efritz09/washiato/Embedded/Washing Cycle Data/Inst_x.png

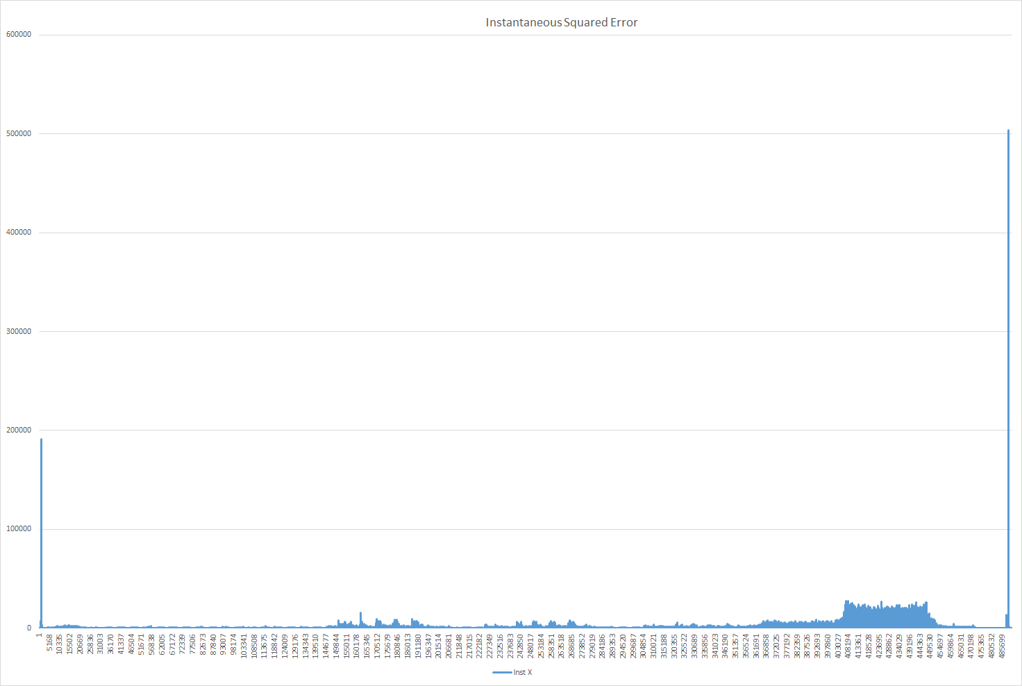
Embedded/Washing Cycle Data/Inst_x.png
