efritz09/washiato/Mechanical Design/COMMUNAL_PARTS/WIFI_HUZZAH.SLDPRT

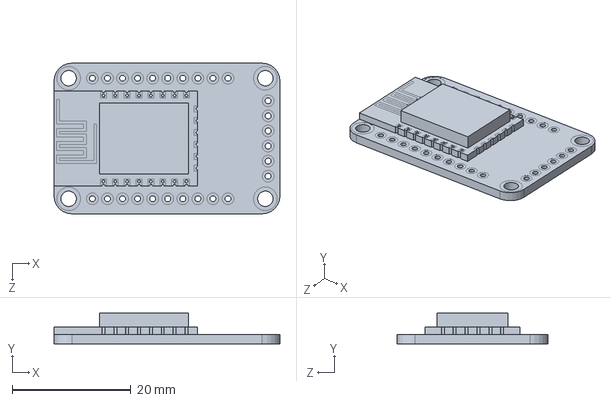
[picture p22: CAD file, 2016-05-10]
Mechanical Design/COMMUNAL_PARTS/WIFI_HUZZAH.SLDPRT
38.1 x 5.18 x 25.4 mm
