efritz09/washiato/Deliverables/CAD/TOP.SLDPRT

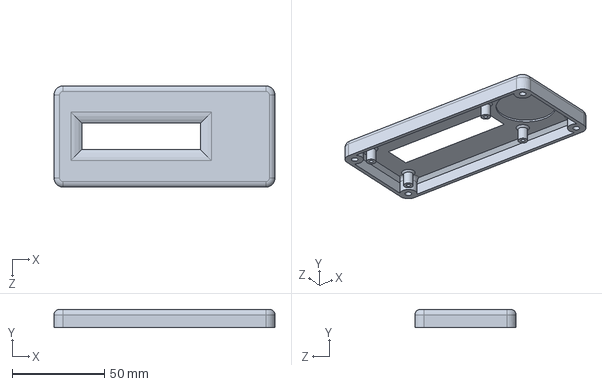
[picture p23: CAD file, 2016-06-02]
Deliverables/CAD/TOP.SLDPRT
120.0 x 10.0 x 55.0 mm
