efritz09/washiato/Mechanical Design/COMMUNAL_PARTS/POLOLU_U3V12F5.SLDPRT

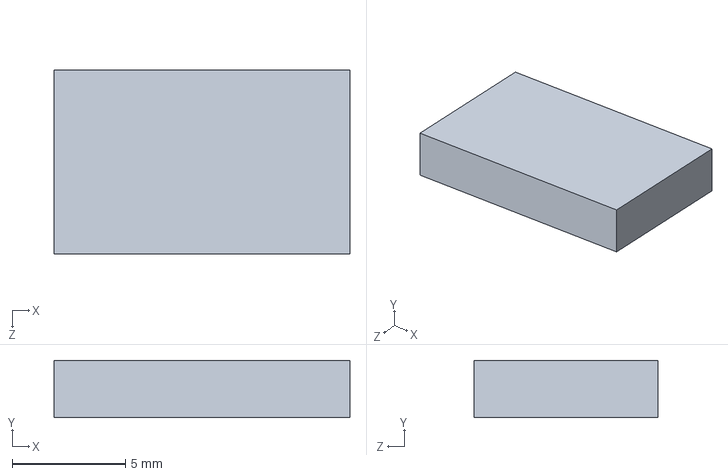
[picture p24: CAD file, 2016-05-10]
Mechanical Design/COMMUNAL_PARTS/POLOLU_U3V12F5.SLDPRT
13.1 x 2.54 x 8.13 mm
