efritz09/washiato/Mechanical Design/COMMUNAL_PARTS/LIMIT_SWITCH.SLDPRT

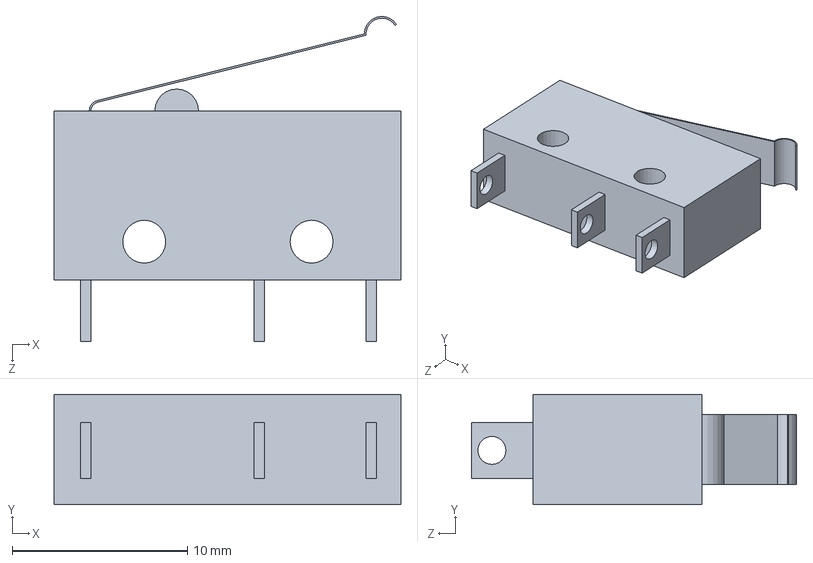
[picture p25: CAD file, 2016-05-10]
Mechanical Design/COMMUNAL_PARTS/LIMIT_SWITCH.SLDPRT
19.8 x 6.30 x 18.6 mm
