efritz09/washiato/Deliverables/CAD/PIN.SLDPRT

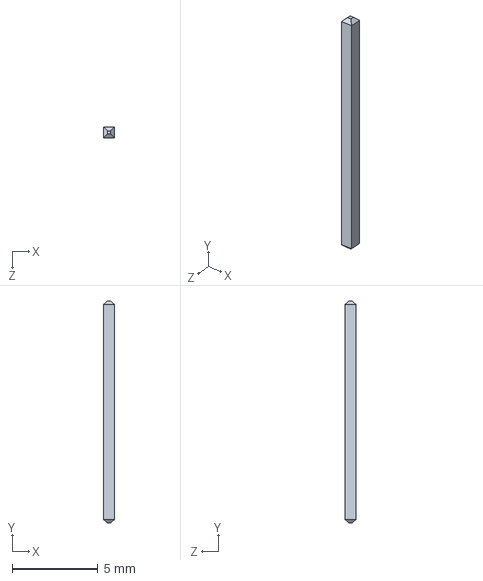
[picture p26: CAD file, 2016-06-02]
Deliverables/CAD/PIN.SLDPRT
0.64 x 12.9 x 0.64 mm
