efritz09/washiato/Deliverables/CAD/BASE.SLDPRT

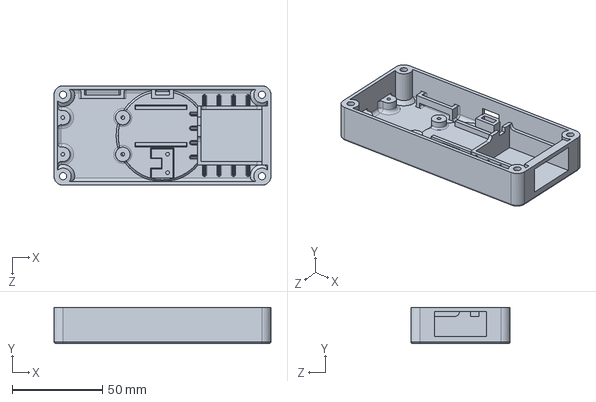
[picture p27: CAD file, 2016-06-02]
Deliverables/CAD/BASE.SLDPRT
120.0 x 20.0 x 55.0 mm
