efritz09/washiato/Deliverables/CAD/SPARKFUN_MMA8452Q_BOARD.SLDPRT

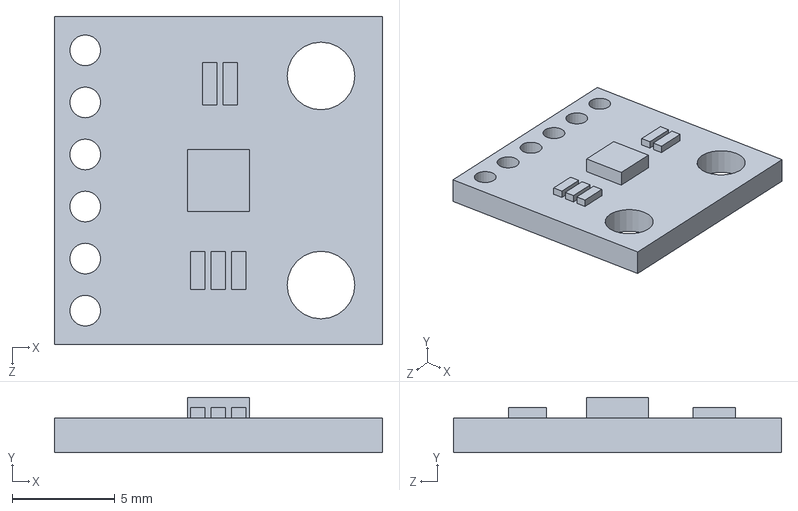
[picture p28: CAD file, 2016-06-02]
Deliverables/CAD/SPARKFUN_MMA8452Q_BOARD.SLDPRT
16.0 x 2.70 x 16.0 mm
