efritz09/washiato/Deliverables/CAD/PIN_HEADER.SLDPRT

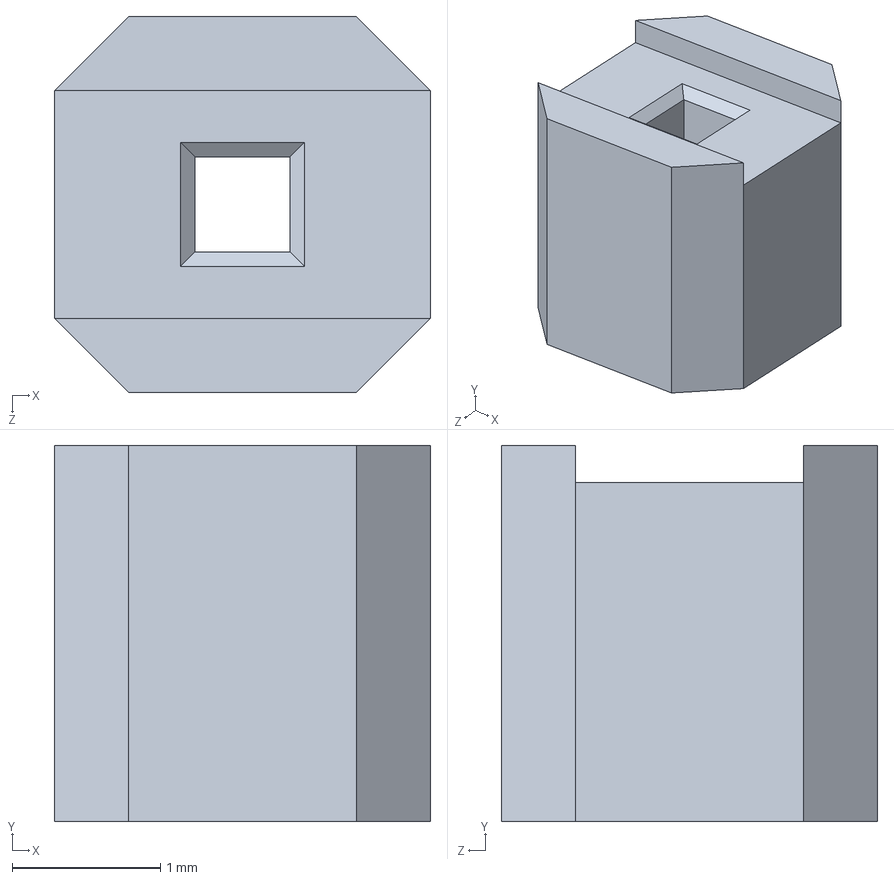
[picture p29: CAD file, 2016-06-02]
Deliverables/CAD/PIN_HEADER.SLDPRT
2.54 x 2.54 x 2.54 mm
