efritz09/washiato/Deliverables/CAD/BATTERY_COVER.SLDPRT

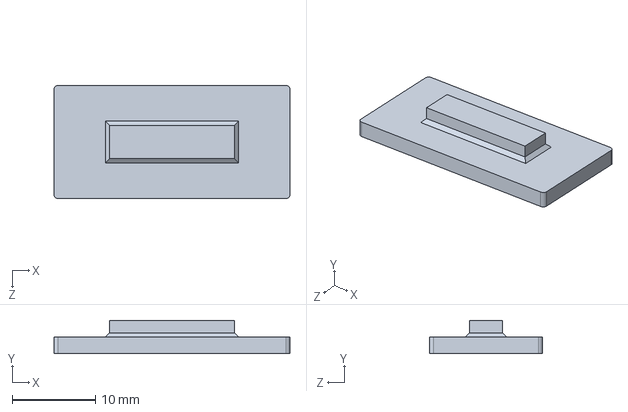
[picture p30: CAD file, 2016-06-02]
Deliverables/CAD/BATTERY_COVER.SLDPRT
28.3 x 4.00 x 13.6 mm
