efritz09/washiato/Deliverables/CAD/MAGNET.SLDPRT

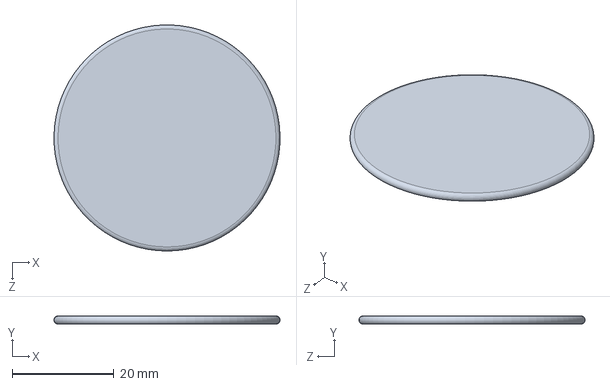
[picture p31: CAD file, 2016-05-10]
Deliverables/CAD/MAGNET.SLDPRT
44.5 x 1.60 x 44.5 mm
