efritz09/washiato/Deliverables/CAD/NFC_TAG.SLDPRT

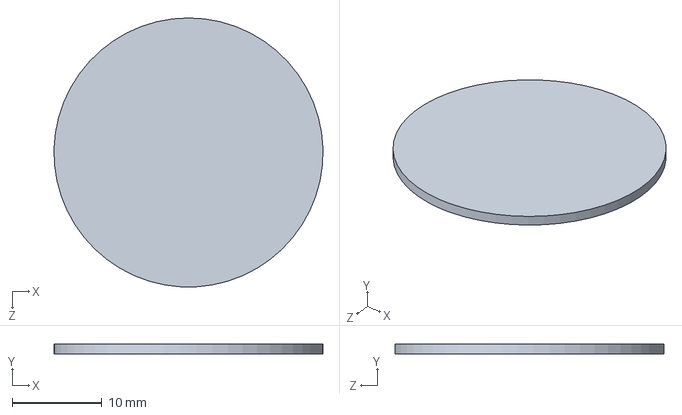
[picture p32: CAD file, 2016-05-10]
Deliverables/CAD/NFC_TAG.SLDPRT
30.0 x 1.10 x 30.0 mm
